r-ismer/Temperature-sensor/Software/app/Include/main.h

// **********************************************************************************************************
// File name    : main.h                                                                                    *
// Author       : Richard I.                                                                                * 
// Date         : 30/01/2026                                                                                *
// Description  : Main file                                                                                 *
// **********************************************************************************************************
# ifndef _MAIN_H_
# define _MAIN_H_ 

// **********************************************************************************************************
//                                               Include                                                    *
// **********************************************************************************************************
#include "definitions.h"
#include "stm32f0xx_hal.h"  
#include "hw_config.h"  

// **********************************************************************************************************
//                                           Public fuctions                                                *
// **********************************************************************************************************
// **********************************************************************************************************
// Function name    : main                                                                                  *
// Description      : Main function.                                                                        *
// Argument         : None                                                                                  *
// Return value     : int                                                                                   *
// **********************************************************************************************************
int main(void);

// **********************************************************************************************************
// Function name    : error_handler                                                                         *
// Description      : Error handler function.                                                               *
// Argument         : None                                                                                  *
// Return value     : None                                                                                  *
// **********************************************************************************************************
void error_handler(void);

// **********************************************************************************************************
// Function name    : assert_failed                                                                         *
// Description      : Assert failed function.                                                               *
// Argument         : file: Pointer to the source file name                                                 *
//                  : line: assert_param error line source number                                           *
// Return value     : None                                                                                  *
// **********************************************************************************************************
void assert_failed(uint8_t* file, uint32_t line);

# endif // _MAIN_H_
