r-ismer/Temperature-sensor/Software/app/Include/task.h

// **********************************************************************************************************
// File name    : task.h                                                                                    *
// Author       : Richard I.                                                                                * 
// Date         : 03/02/2026                                                                                *
// Description  : Task executed to capture the temperature and humidity and send them                       *
// **********************************************************************************************************
# ifndef _TASK_H_
# define _TASK_H_ 

// **********************************************************************************************************
//                                               Include                                                    *
// **********************************************************************************************************
#include "definitions.h"
#include "main.h"

// **********************************************************************************************************
//                                           Public fuctions                                                *
// **********************************************************************************************************
// **********************************************************************************************************
// Function name    : task_init                                                                             *
// Description      : Initialize the sendor driver                                                          *
// Argument         : None                                                                                  *
// Return value     : None                                                                                  *
// **********************************************************************************************************
void task_init(void);

// **********************************************************************************************************
// Function name    : task                                                                                  *
// Description      : Task executed to capture the temperature and humidity and send them                   *
// Argument         : None                                                                                  *
// Return value     : Noe                                                                                   *
// **********************************************************************************************************
void task(void);

# endif // _TASK_H_
